uStepper/uStepper-RobotArm-Rev3/STL_files/spacer_M4_short.stl

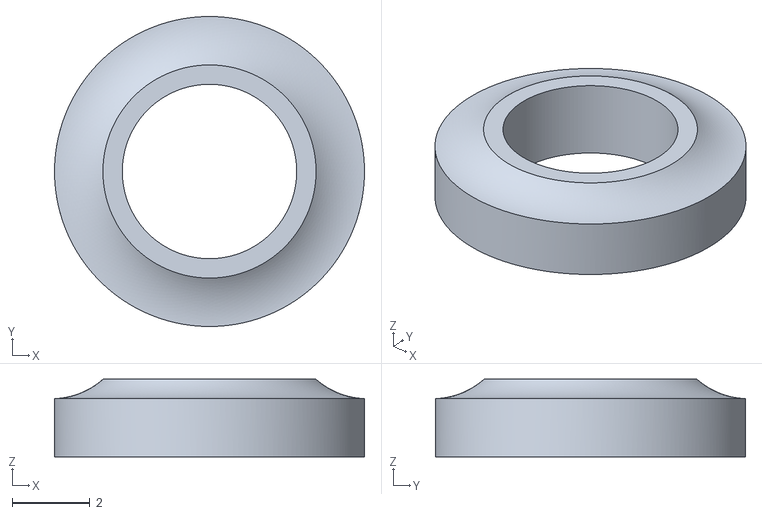
[picture p15: CAD file, 2016-12-30]
STL_files/spacer_M4_short.stl
8.00 x 8.00 x 2.00
