uStepper/uStepper-RobotArm-Rev3/STL_files/Gears_second_arm-Biggear.stl

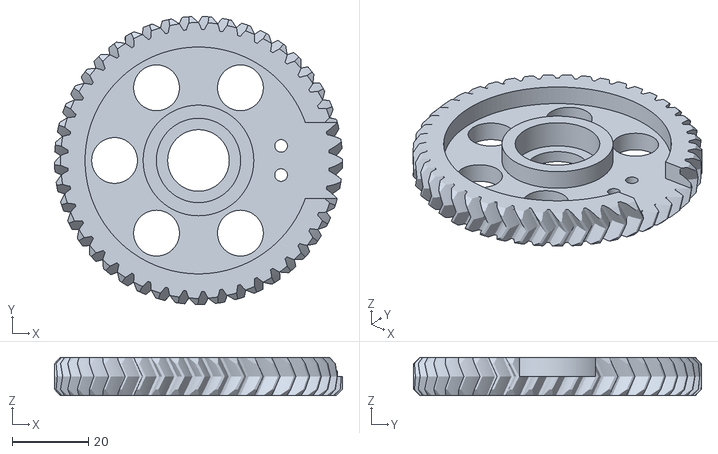
[picture p16: CAD file, 2016-12-30]
STL_files/Gears_second_arm-Biggear.stl
75.5 x 75.5 x 10.0
