uStepper/uStepper-RobotArm-Rev3/STL_files/spacer_M8_long.stl

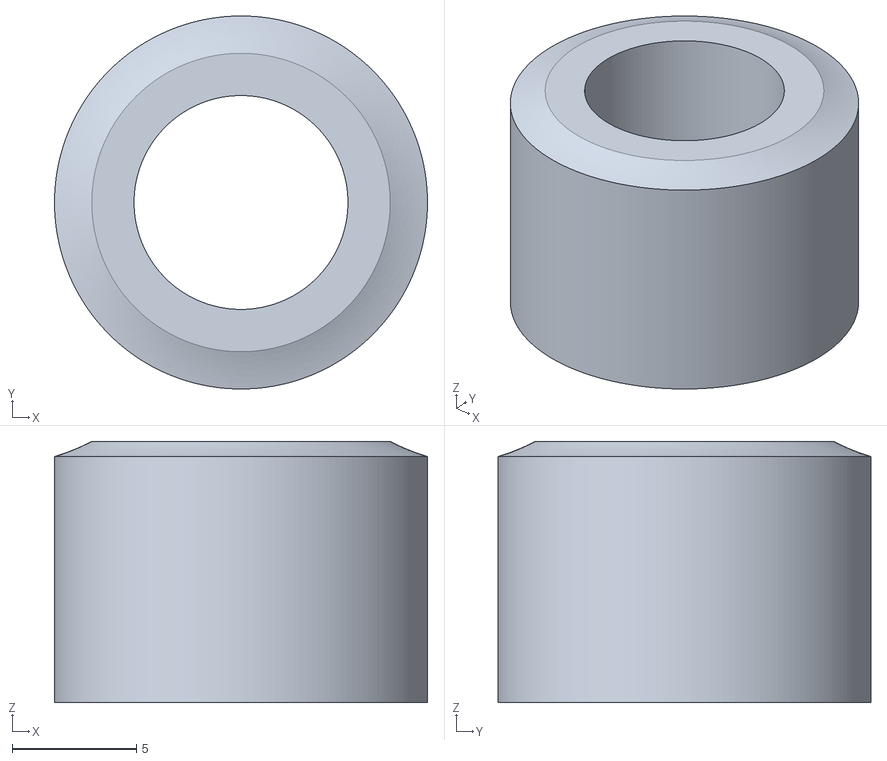
[picture p17: CAD file, 2016-12-30]
STL_files/spacer_M8_long.stl
15.0 x 15.0 x 10.5
