uStepper/uStepper-RobotArm-Rev3/STL_files/spacer_M4_long.stl

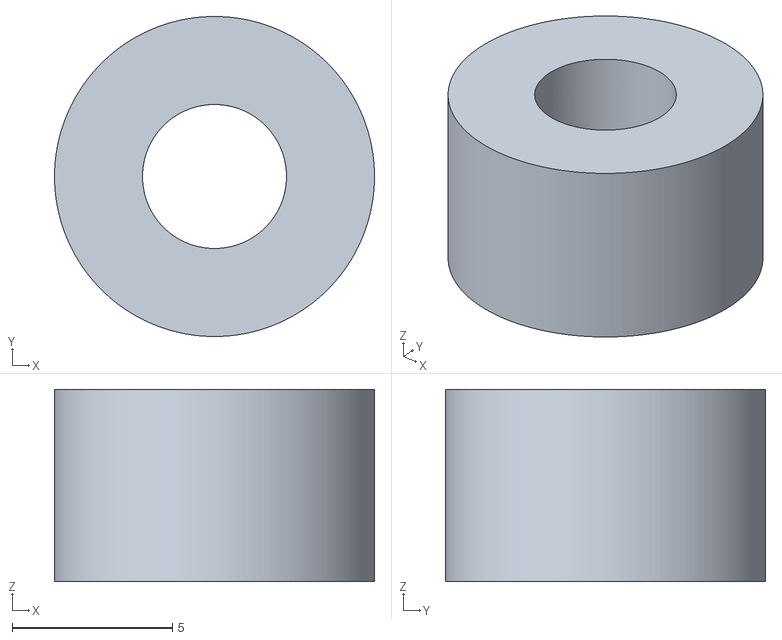
[picture p18: CAD file, 2016-12-30]
STL_files/spacer_M4_long.stl
10.00 x 10.0 x 6.00
