uStepper/uStepper-RobotArm-Rev3/STL_files/Gears_second_arm_smallGear.stl

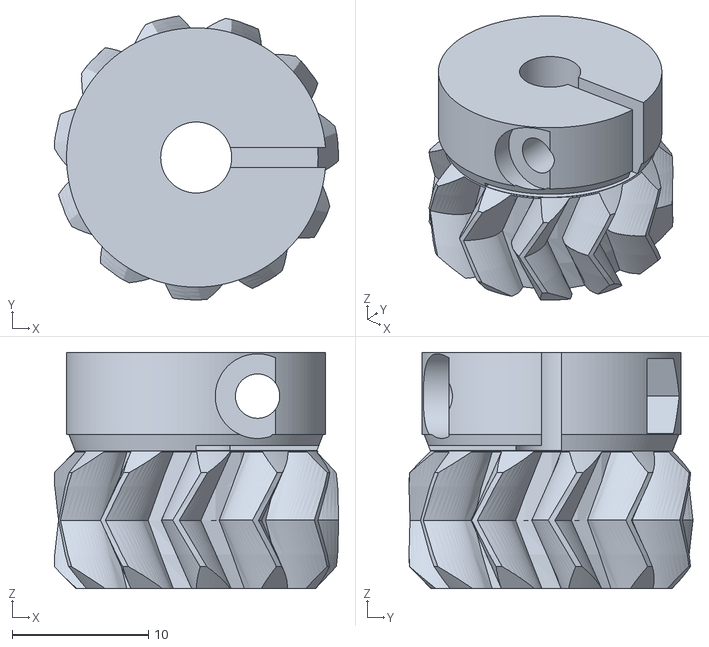
[picture p19: CAD file, 2016-12-30]
STL_files/Gears_second_arm_smallGear.stl
20.8 x 20.8 x 17.3
