uStepper/uStepper-RobotArm-Rev3/STL_files/side2.stl

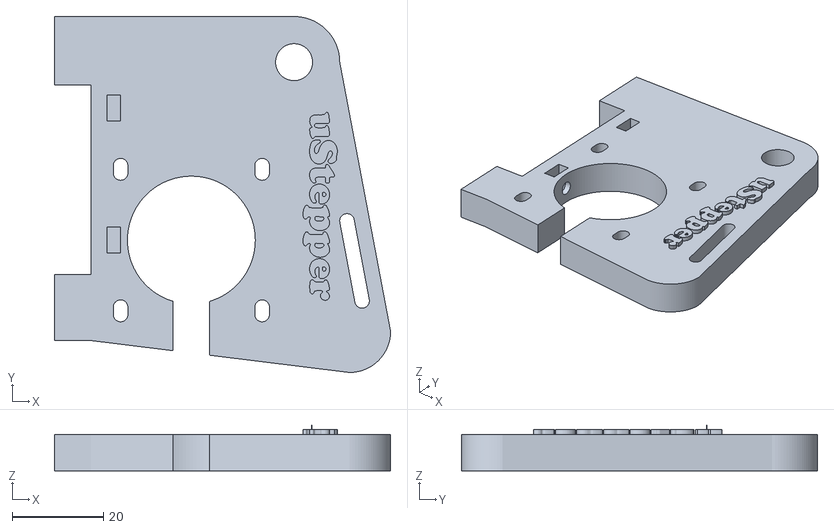
[picture p20: CAD file, 2016-12-30]
STL_files/side2.stl
73.6 x 78.0 x 10.00
