uStepper/uStepper-RobotArm-Rev3/STL_files/baseplate.stl

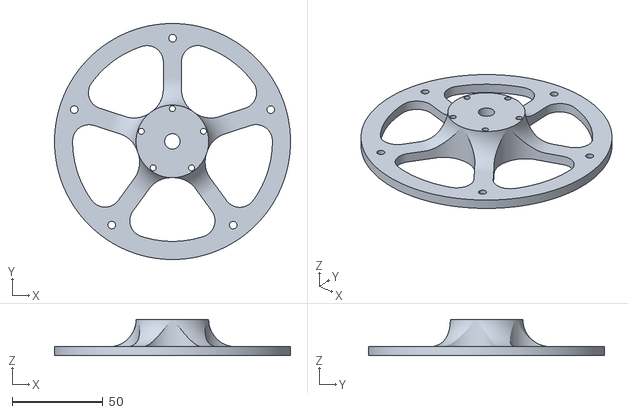
[picture p21: CAD file, 2016-12-30]
STL_files/baseplate.stl
130.0 x 130.0 x 20.0
