uStepper/uStepper-RobotArm-Rev3/STL_files/bottom.stl

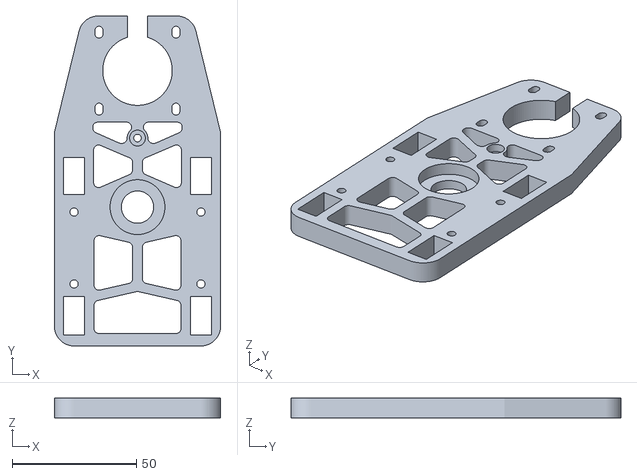
[picture p22: CAD file, 2016-12-30]
STL_files/bottom.stl
67.0 x 133.0 x 8.00
