uStepper/uStepper-RobotArm-Rev3/STL_files/rod_end_15mm.stl

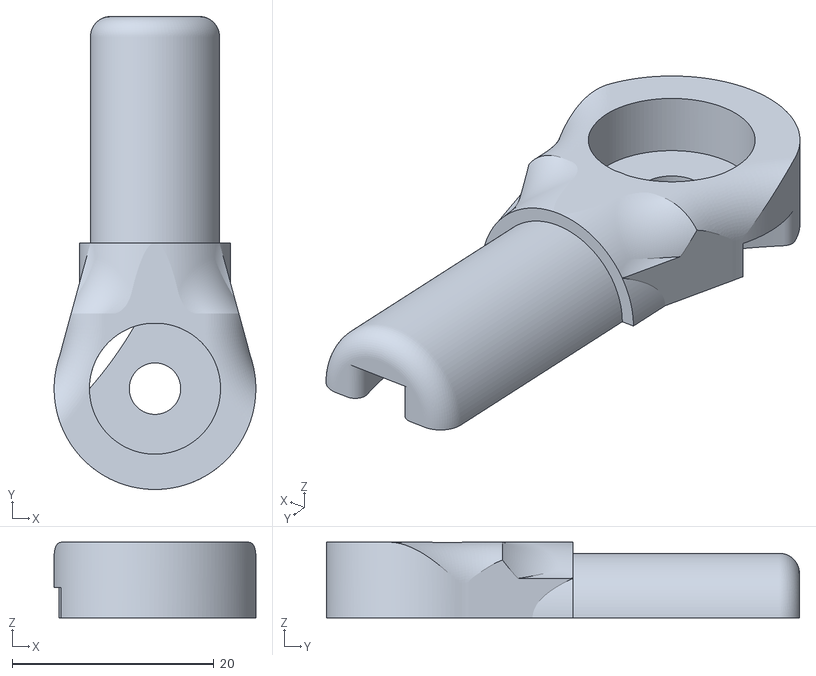
[picture p23: CAD file, 2016-12-30]
STL_files/rod_end_15mm.stl
20.0 x 46.9 x 7.50
