uStepper/uStepper-RobotArm-Rev3/STL_files/second_gear_arm.stl

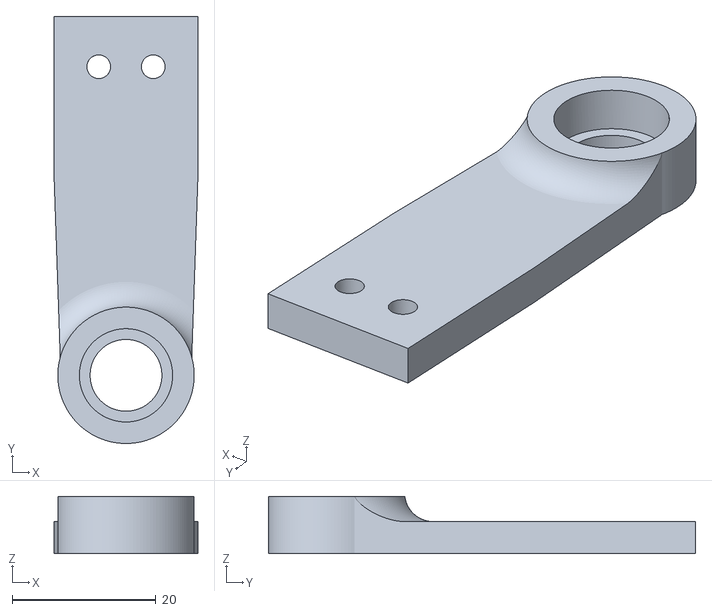
[picture p25: CAD file, 2016-12-30]
STL_files/second_gear_arm.stl
20.0 x 59.5 x 8.00
