uStepper/uStepper-RobotArm-Rev3/STL_files/endtriangle2_rev2.stl

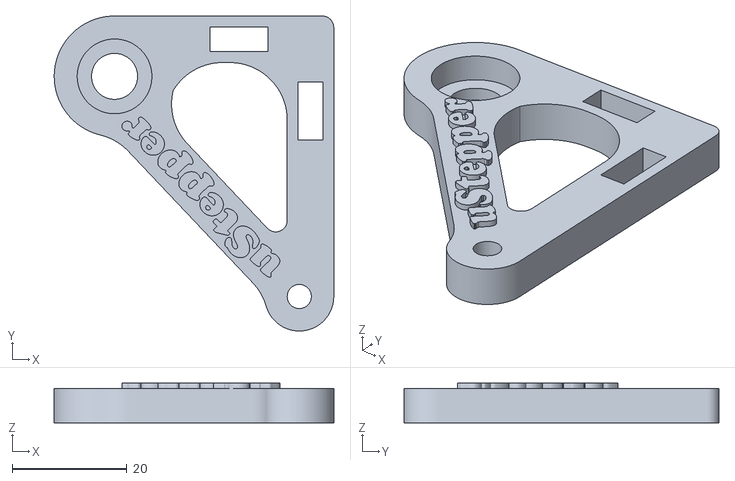
[picture p26: CAD file, 2016-12-30]
STL_files/endtriangle2_rev2.stl
48.6 x 54.8 x 6.90
