uStepper/uStepper-RobotArm-Rev3/STL_files/spacer_M8_short.stl

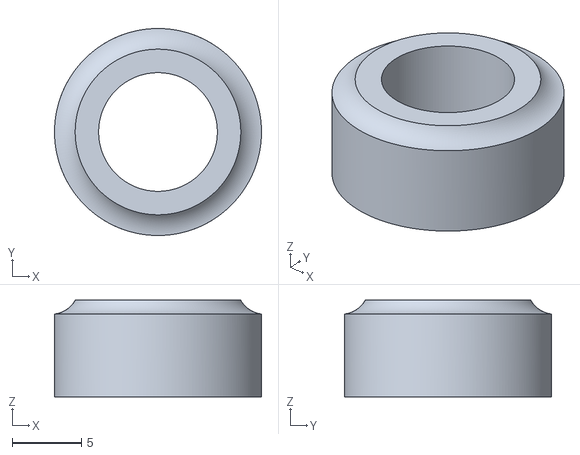
[picture p27: CAD file, 2016-12-30]
STL_files/spacer_M8_short.stl
15.0 x 15.0 x 7.00
