uStepper/uStepper-RobotArm-Rev3/STL_files/link.stl

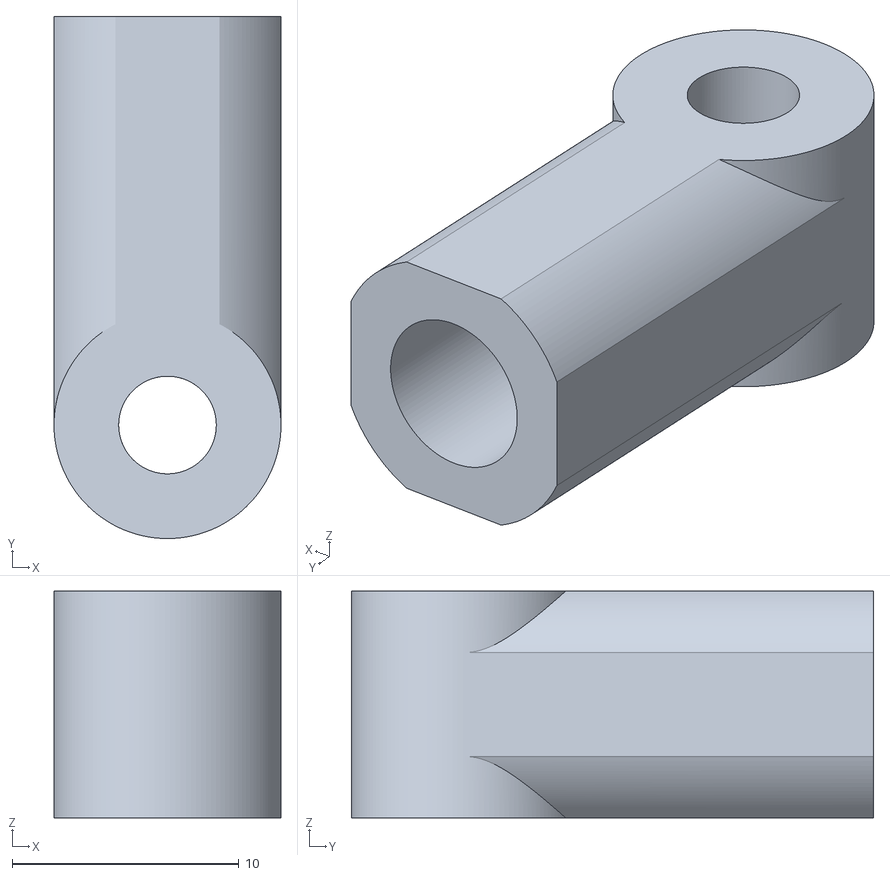
[picture p28: CAD file, 2016-12-30]
STL_files/link.stl
10.0 x 23.0 x 10.0
