uStepper/uStepper-RobotArm-Rev3/STL_files/triangle.stl

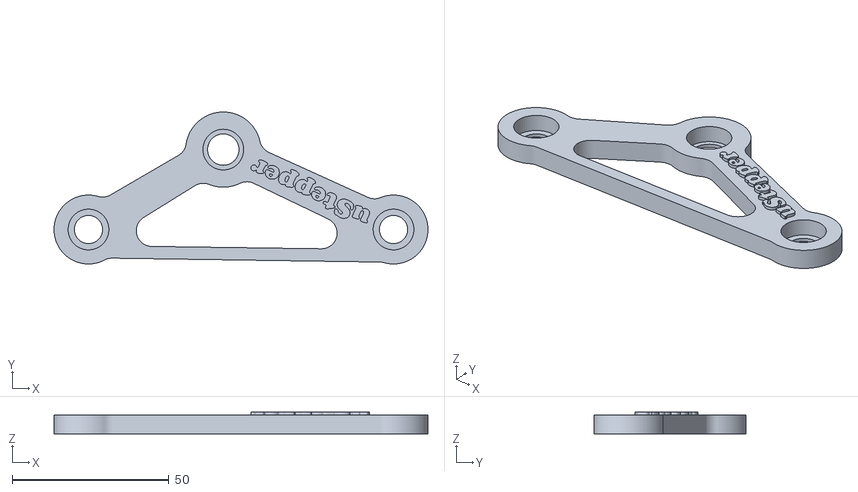
[picture p29: CAD file, 2016-12-30]
STL_files/triangle.stl
119.3 x 48.5 x 6.90
